SarusanS/Smart-Water-Bottle/RendersImaes_2/10.png

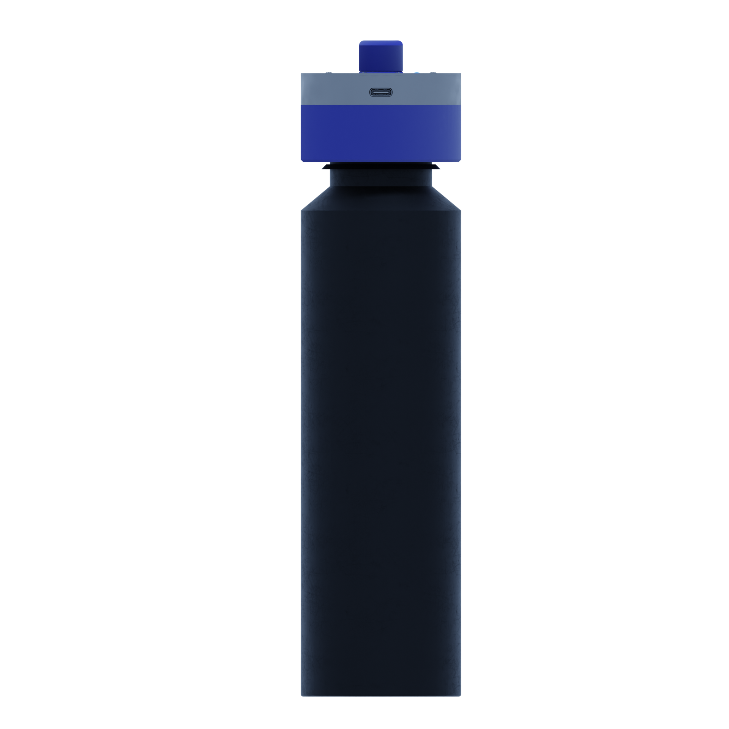
RendersImaes_2/10.png
