SarusanS/Smart-Water-Bottle/RendersImaes_2/12.png

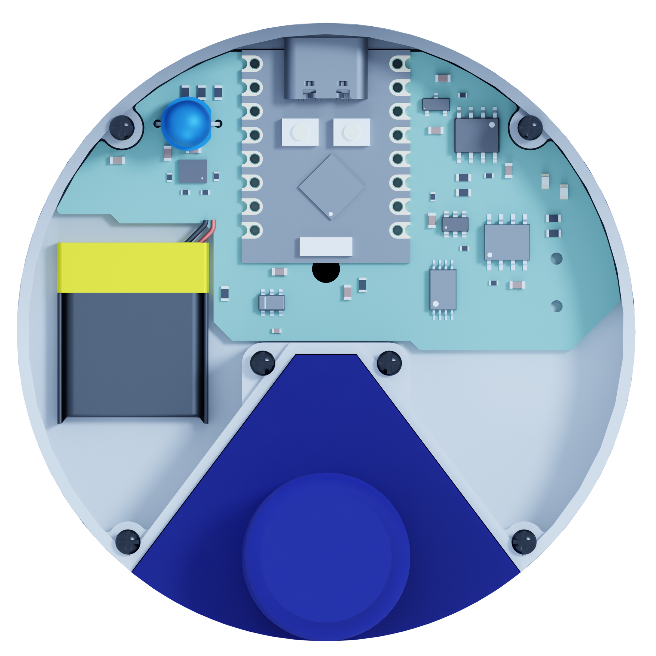
RendersImaes_2/12.png
