SarusanS/Smart-Water-Bottle/RendersImaes_2/13.png

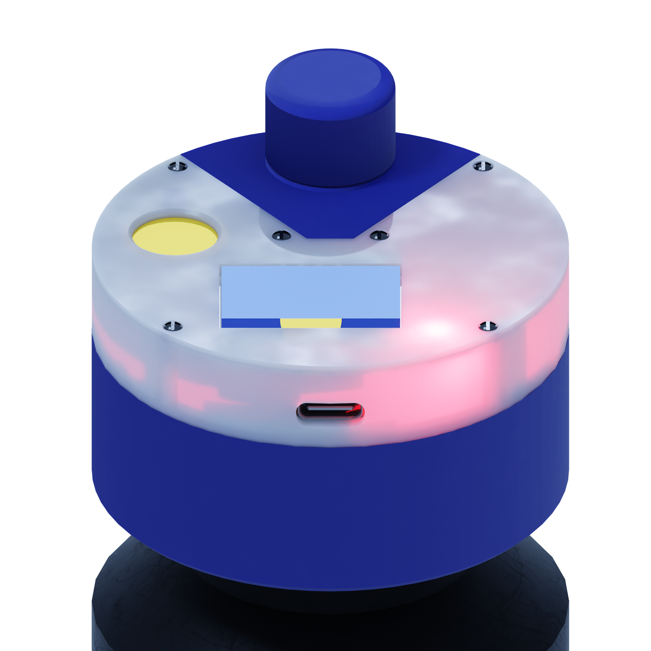
RendersImaes_2/13.png
