SarusanS/Smart-Water-Bottle/RendersImaes_2/14.png

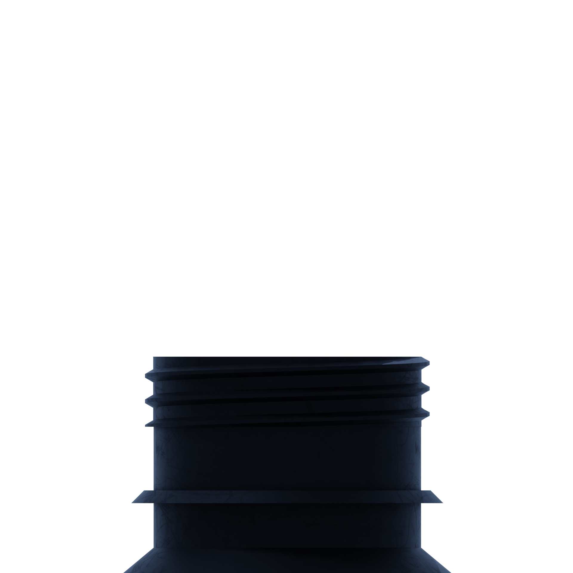
RendersImaes_2/14.png
