SarusanS/Smart-Water-Bottle/RendersImaes_2/15.png

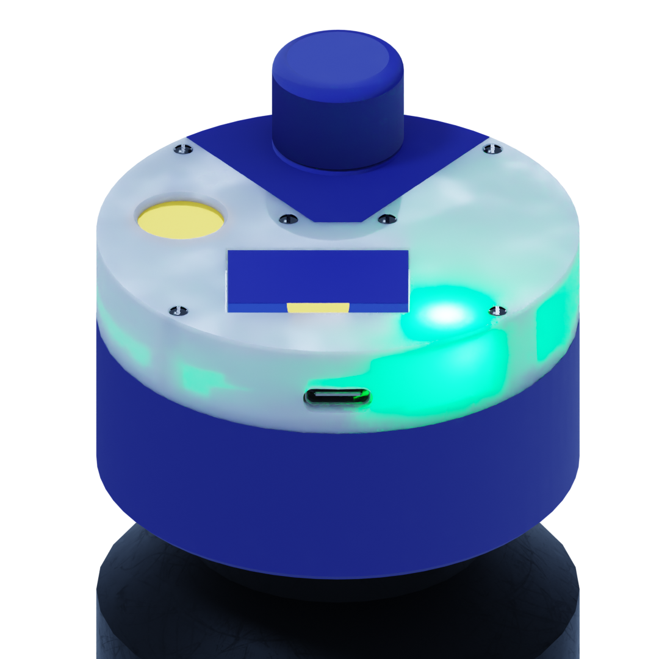
RendersImaes_2/15.png
