SarusanS/Smart-Water-Bottle/RendersImages_1/6_1.png

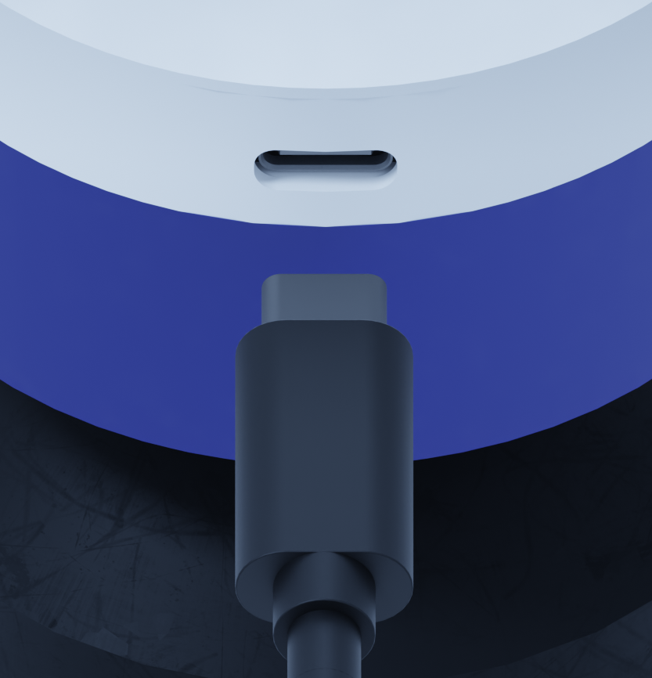
RendersImages_1/6_1.png
