SarusanS/Smart-Water-Bottle/RendersImages_1/7.png

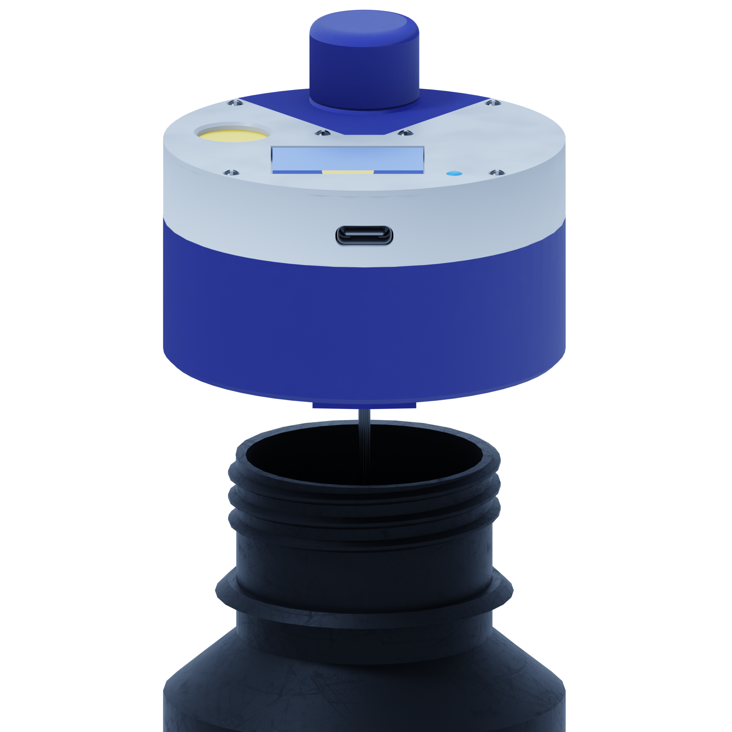
RendersImages_1/7.png
