SarusanS/Smart-Water-Bottle/RendersImages_1/8.png

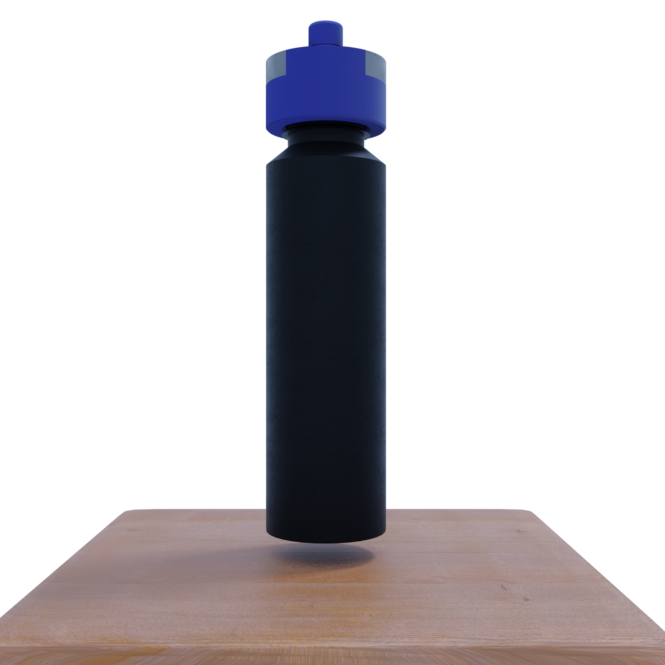
RendersImages_1/8.png
